AyrtonAlef/ZeDrop/Lab-design goniometer/Substrate positioning module/BaseEixoX_Frente.SLDPRT

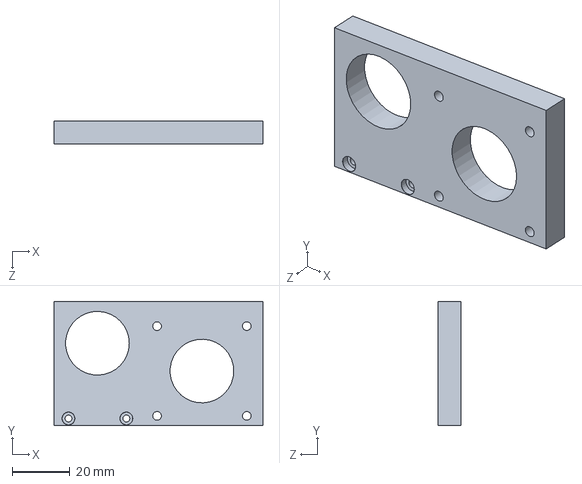
[picture p19: CAD file, 2024-04-06]
Lab-design goniometer/Substrate positioning module/BaseEixoX_Frente.SLDPRT
72.2 x 43.0 x 8.00 mm
