AyrtonAlef/ZeDrop/Lab-design goniometer/Volumetric dispenser/BaseInferior_Impressao_v2.SLDPRT

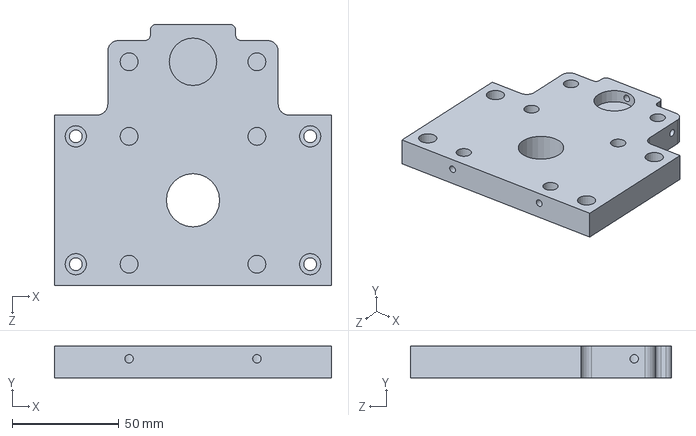
[picture p20: CAD file, 2024-04-06]
Lab-design goniometer/Volumetric dispenser/BaseInferior_Impressao_v2.SLDPRT
130.0 x 15.0 x 122.5 mm
