AyrtonAlef/ZeDrop/Lab-design goniometer/Substrate positioning module/BlocoEixoY.SLDPRT

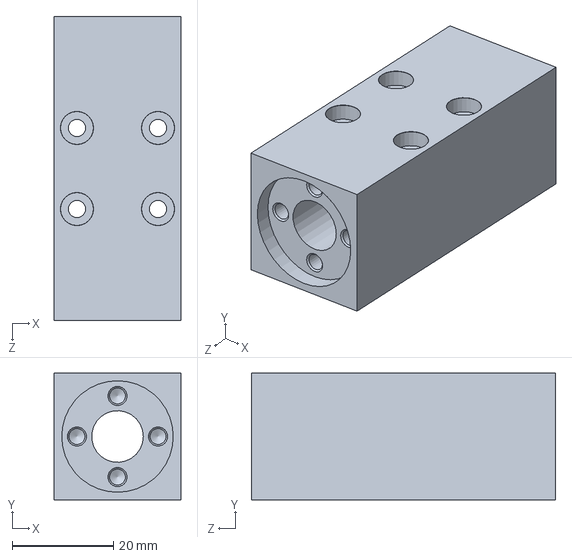
[picture p21: CAD file, 2024-04-06]
Lab-design goniometer/Substrate positioning module/BlocoEixoY.SLDPRT
25.0 x 25.0 x 60.0 mm
