AyrtonAlef/ZeDrop/Lab-design goniometer/Substrate inclination module/Gear_v1.SLDPRT

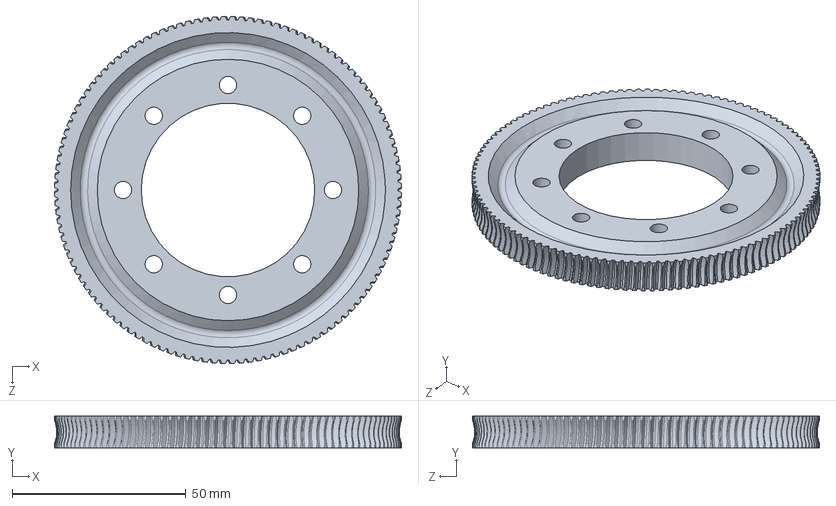
[picture p22: CAD file, 2024-04-06]
Lab-design goniometer/Substrate inclination module/Gear_v1.SLDPRT
100.0 x 9.20 x 100.0 mm
