AyrtonAlef/ZeDrop/Lab-design goniometer/Substrate positioning module/BaseEixoY_Superior2.SLDPRT

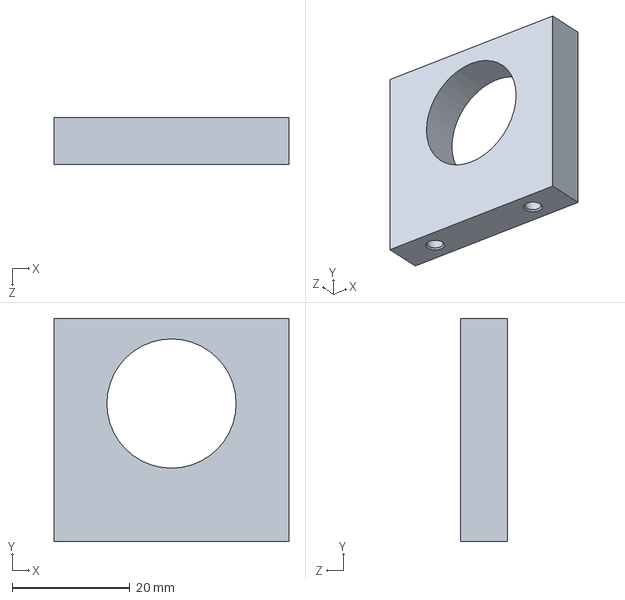
[picture p23: CAD file, 2024-04-06]
Lab-design goniometer/Substrate positioning module/BaseEixoY_Superior2.SLDPRT
40.0 x 38.0 x 8.00 mm
