AyrtonAlef/ZeDrop/Lab-design goniometer/Substrate inclination module/Suporte_amostra.SLDPRT

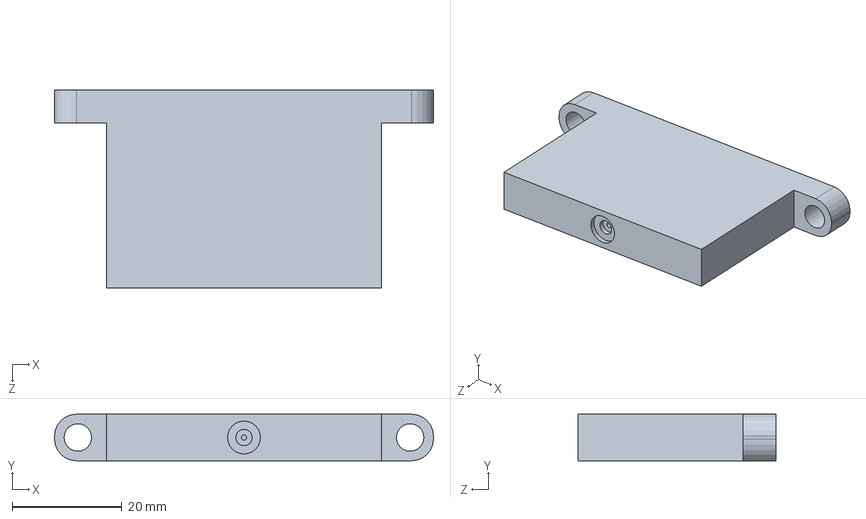
[picture p24: CAD file, 2024-04-06]
Lab-design goniometer/Substrate inclination module/Suporte_amostra.SLDPRT
69.0 x 8.50 x 36.0 mm
