AyrtonAlef/ZeDrop/Lab-design goniometer/Substrate positioning module/BaseEixoX_Fundo.SLDPRT

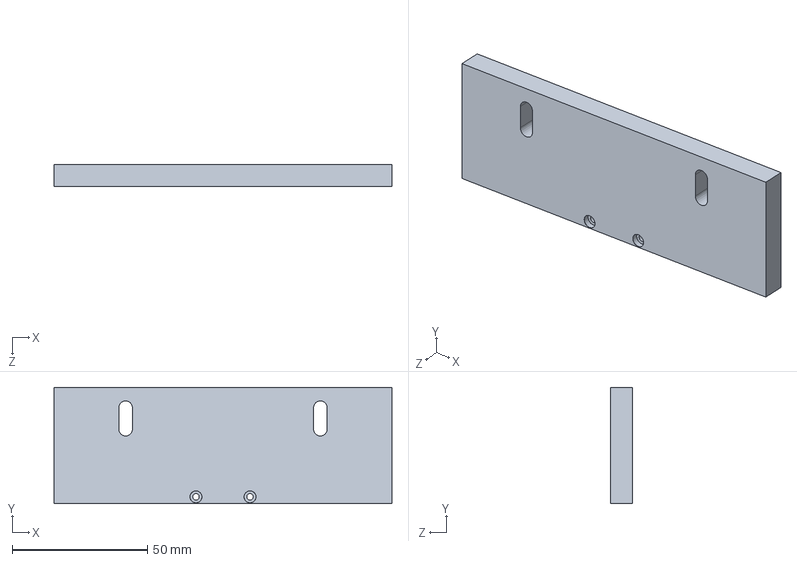
[picture p25: CAD file, 2024-04-06]
Lab-design goniometer/Substrate positioning module/BaseEixoX_Fundo.SLDPRT
125.0 x 43.0 x 8.00 mm
