AyrtonAlef/ZeDrop/Lab-design goniometer/Substrate positioning module/BaseEixoY_Superior1.SLDPRT

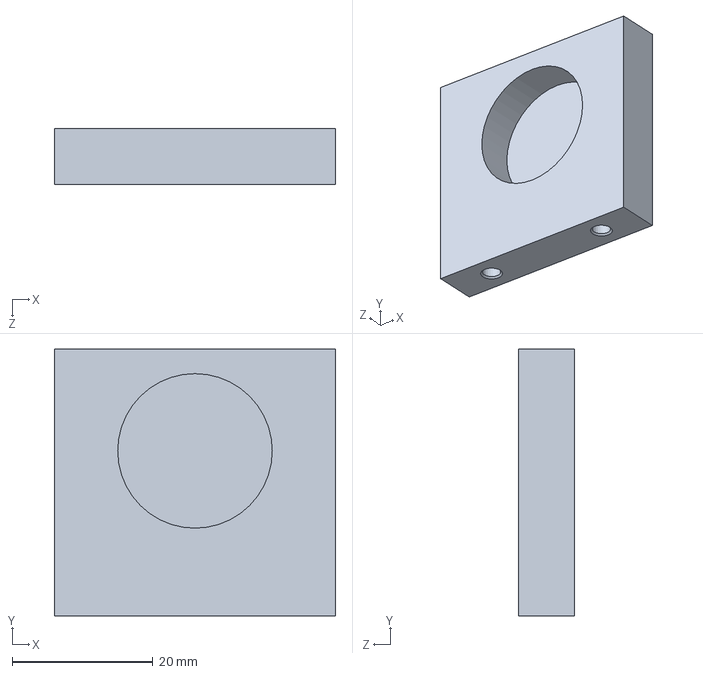
[picture p26: CAD file, 2024-04-06]
Lab-design goniometer/Substrate positioning module/BaseEixoY_Superior1.SLDPRT
40.0 x 38.0 x 8.00 mm
